Jeroen6/IdcProbeV1/doc/RENKFORCE - USB - DC 2.1-5.5mm kabel.pdf

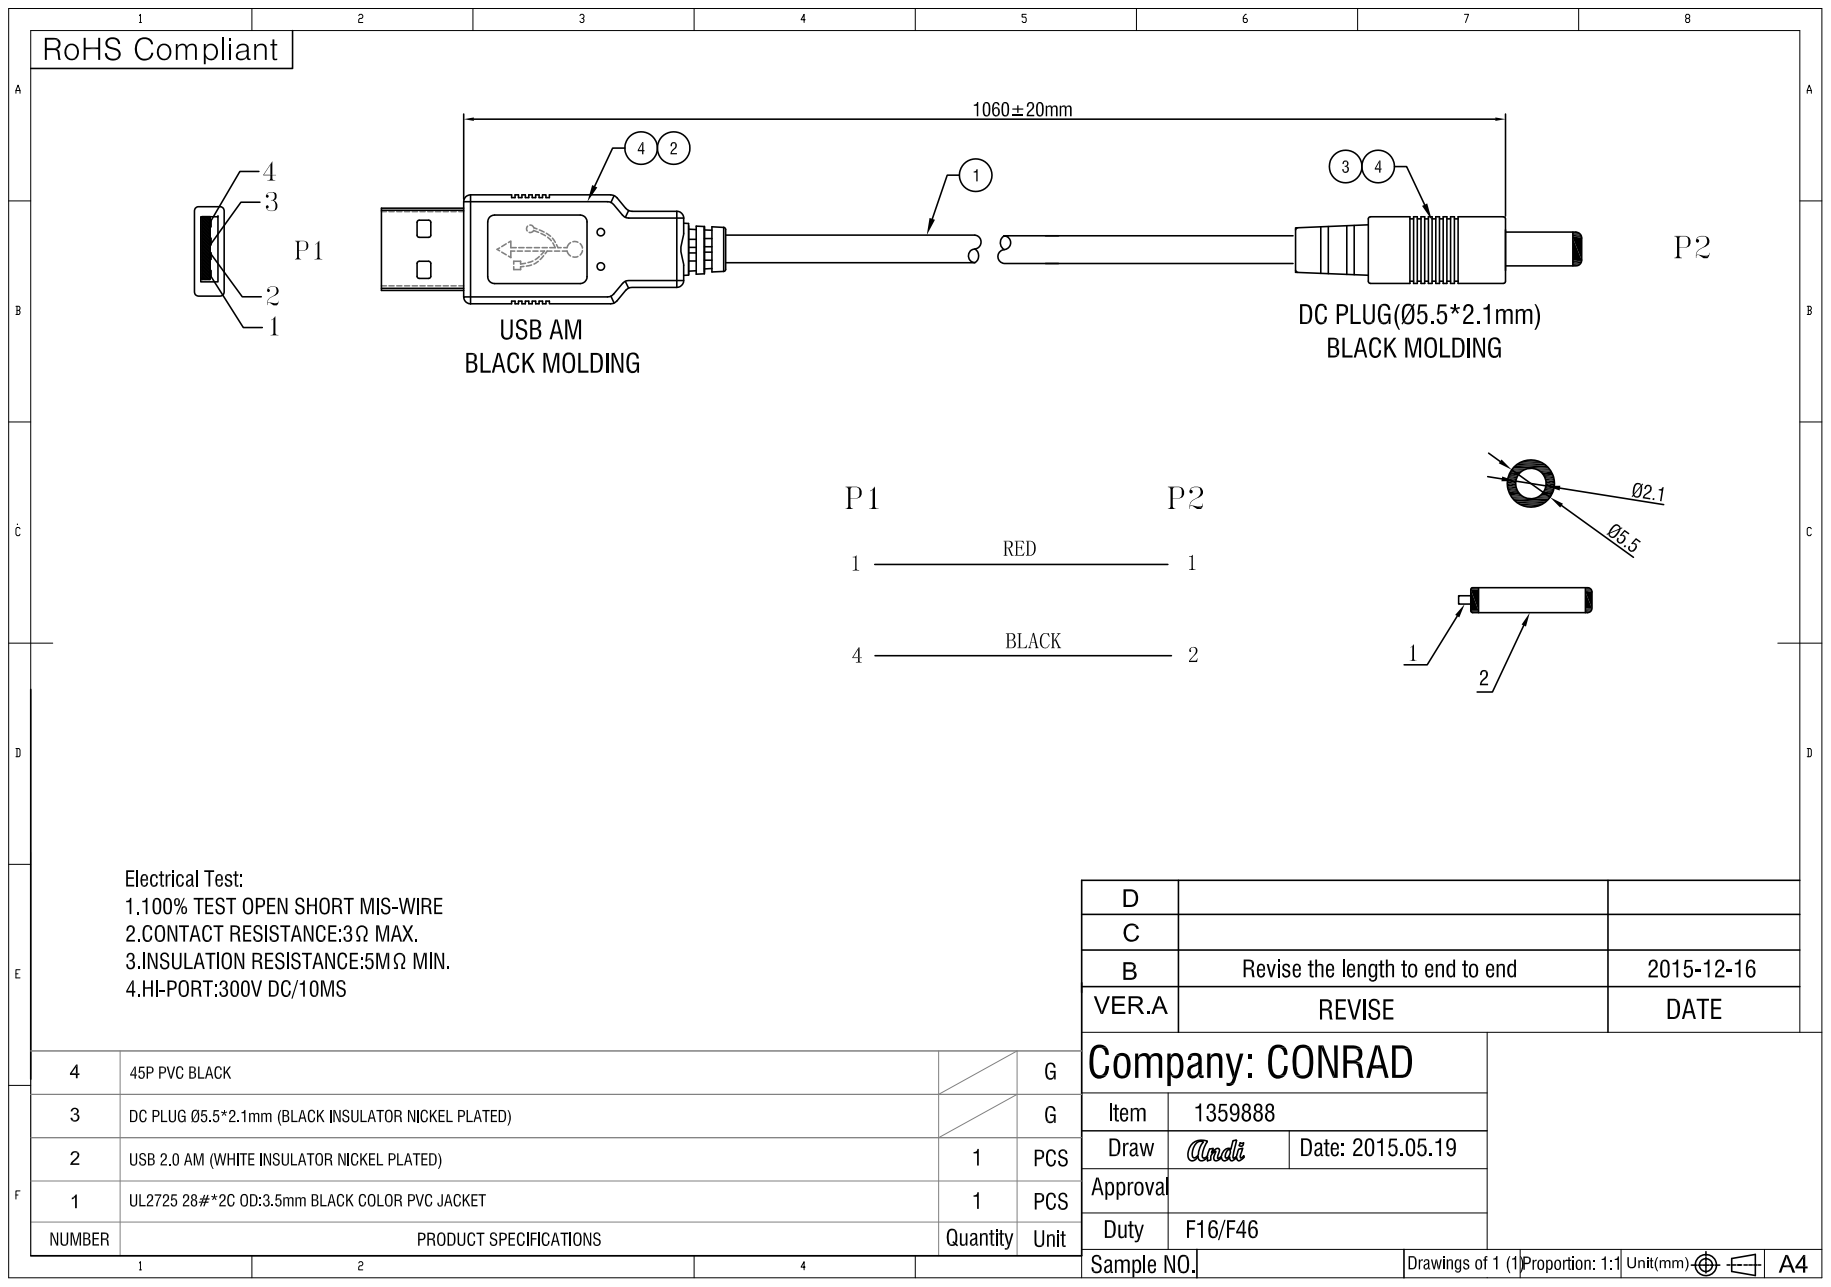
[picture p9: page 1]

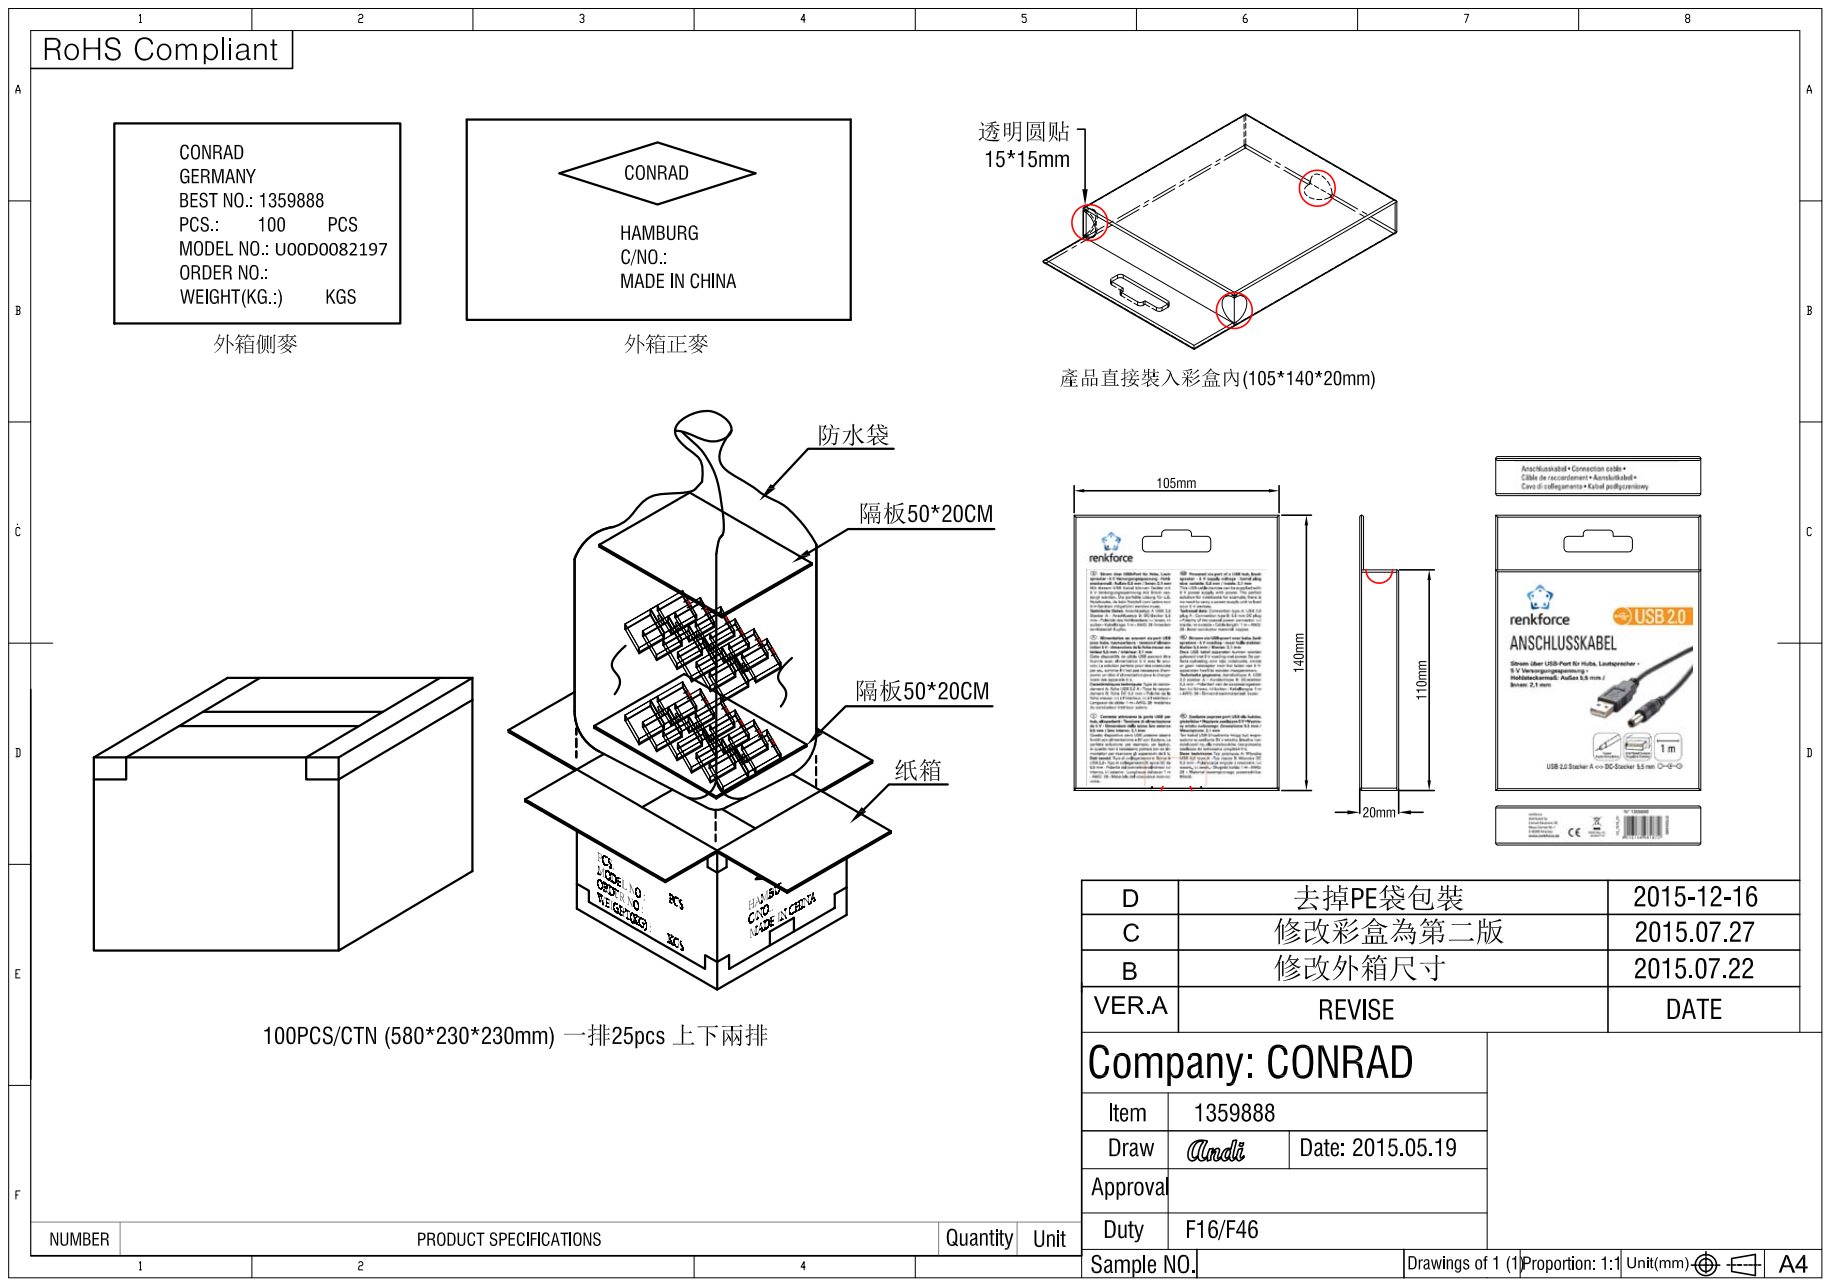
[picture p10: page 2]
