Jeroen6/IdcProbeV1/doc/Telegärtner - J01003A1947 - BNC Connector 50 ohm.pdf

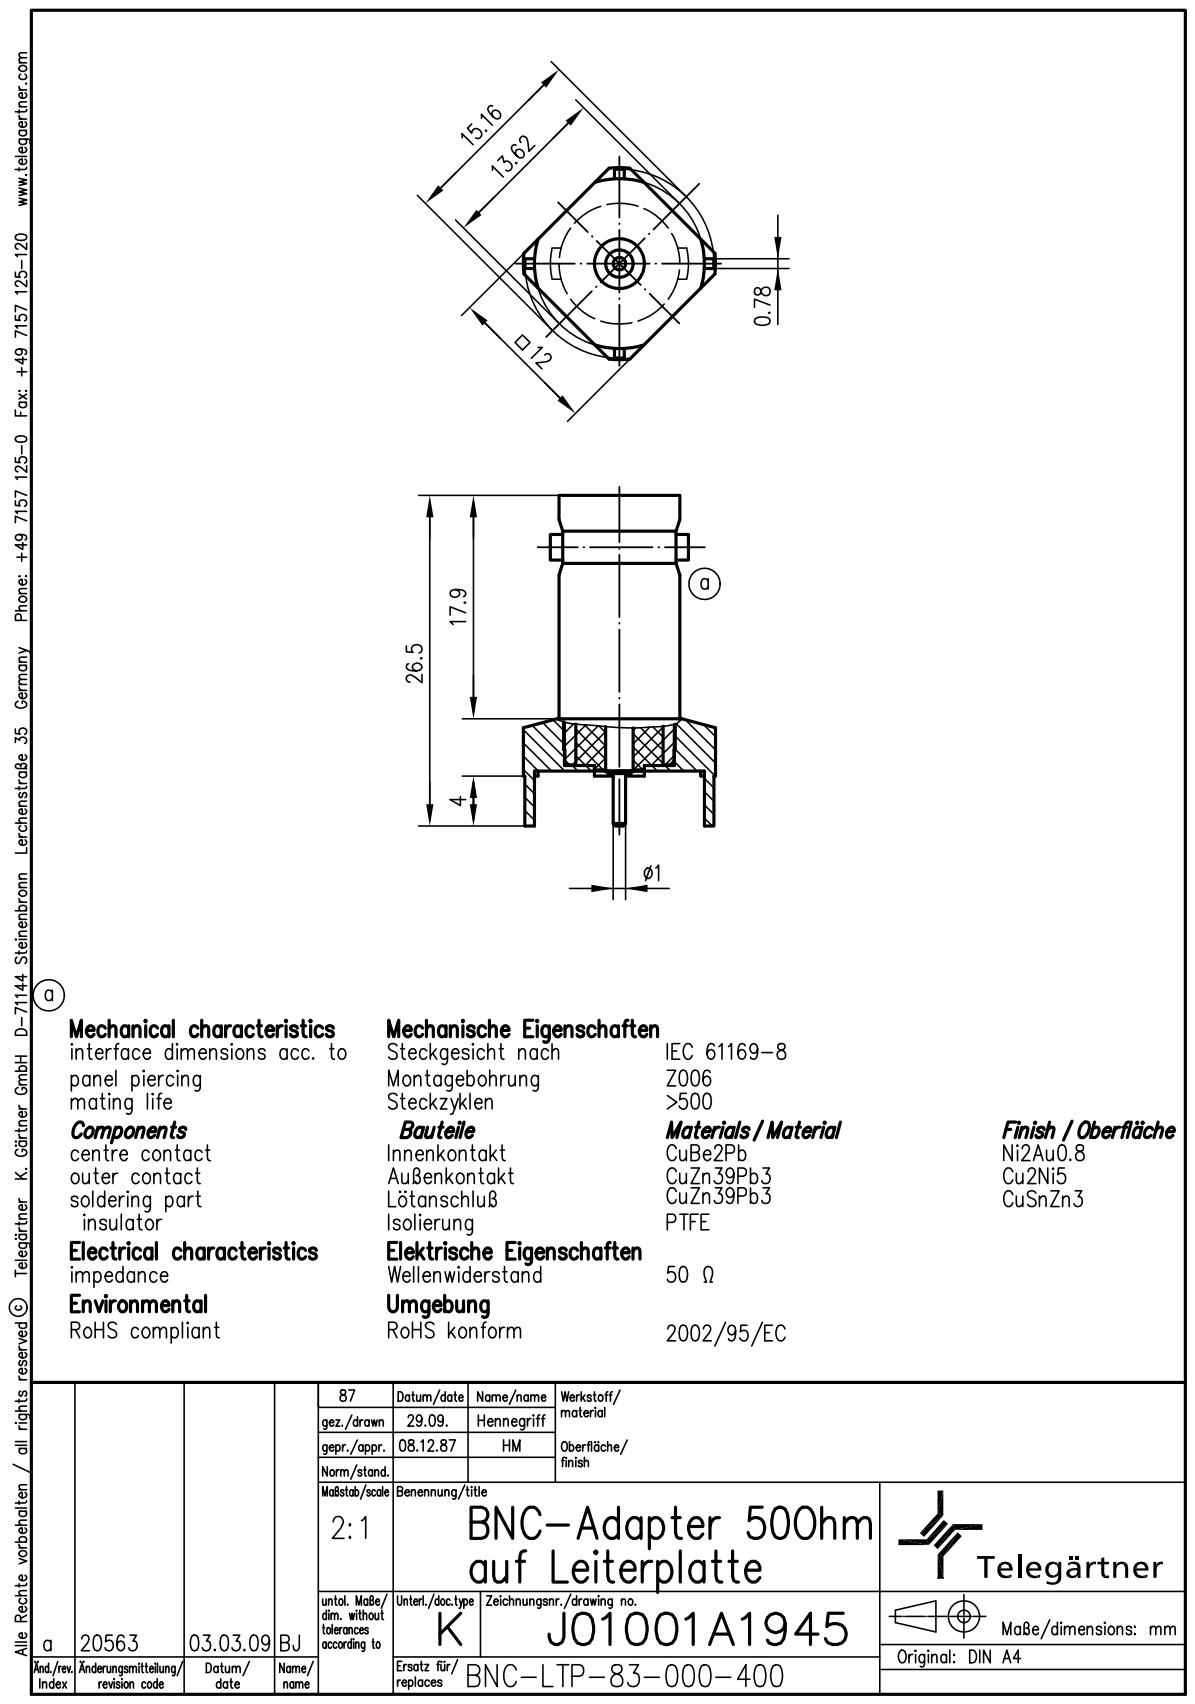
[picture p11: page 1]
