Jeroen6/IdcProbeV1/doc/Telegärtner - J01003A1947 - BNC Connector 75 ohm.pdf

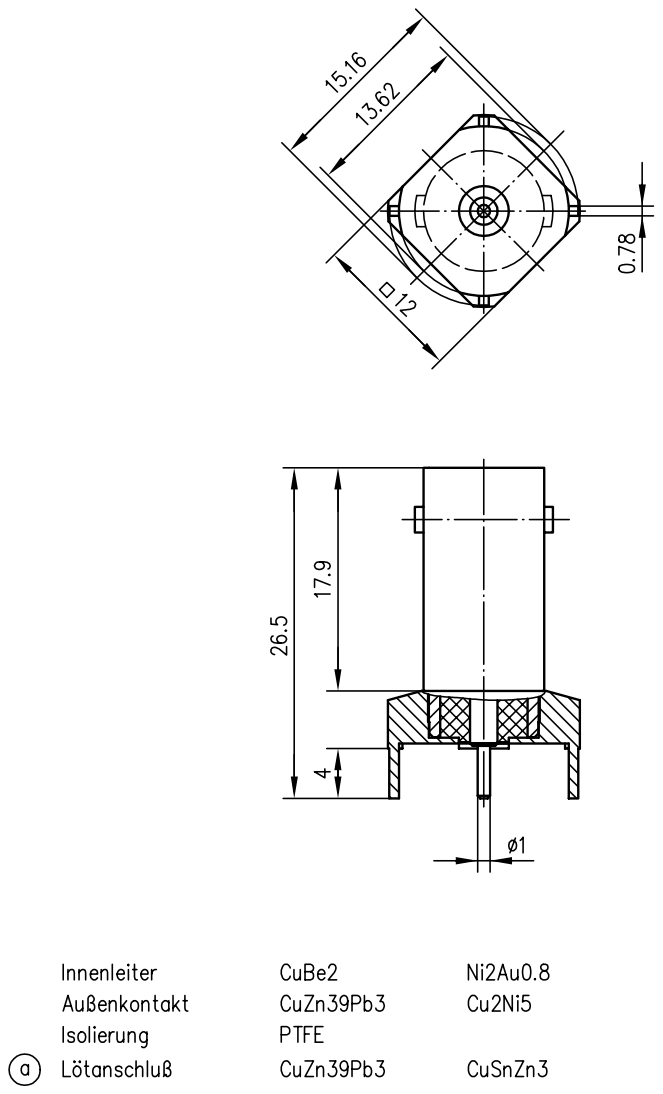
[picture p12: page 1]
