Jeroen6/IdcProbeV1/doc/Telegärtner - J01003A1947 - BNC Connector footprint.pdf

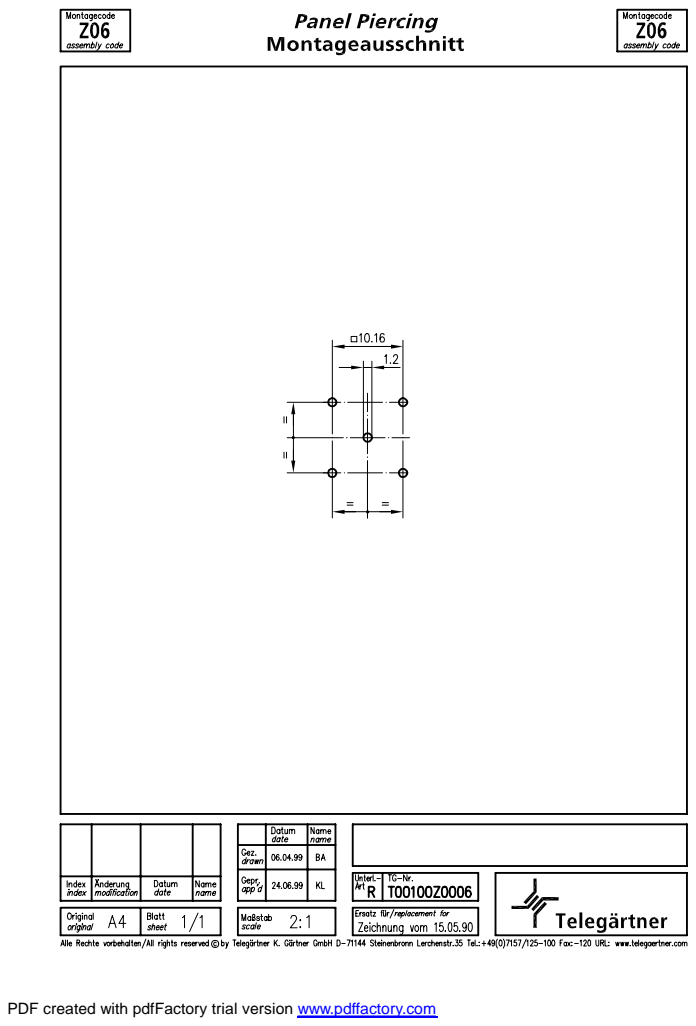
[picture p13: page 1]

PDF created with pdfFactory trial version www.pdffactory.com
